daskals/A-Rectifier-Circuit-Insensitive-to-the-Angle-of-Incidence-of-Incoming-Waves-Based-on-a-Wilkinson/Publication_files/Figures/Fig3-eps-converted-to.pdf

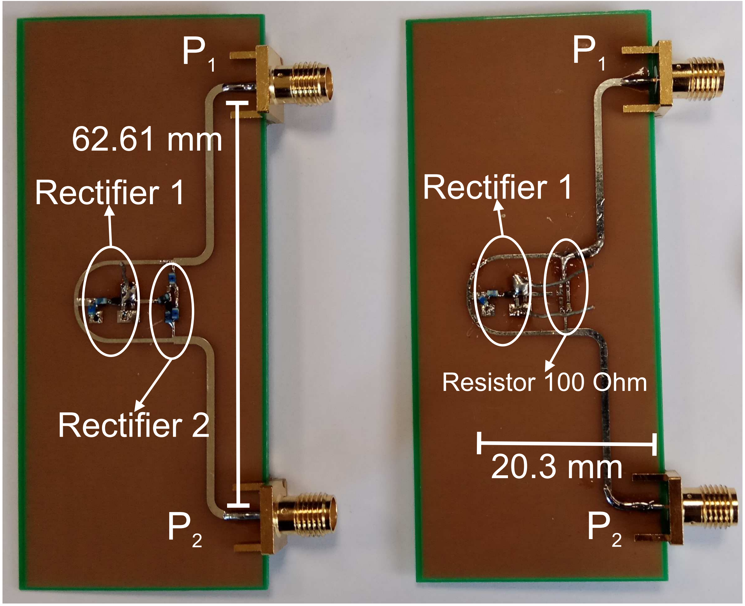
[picture p15: page 1]

Rectifier 1

Rectifier 2

Rectifier 1

Resistor 100 Ohm

62.61 mm

20 3. mm

P1

P2

P1

P2
