daskals/A-Rectifier-Circuit-Insensitive-to-the-Angle-of-Incidence-of-Incoming-Waves-Based-on-a-Wilkinson/Publication_files/Figures/Fig6-eps-converted-to.pdf

-40 | -30 | -20 | -10 | 0 | 10
Power Input (dBm)

0

10

20

30

40

Efficiency (%)
