daskals/A-Rectifier-Circuit-Insensitive-to-the-Angle-of-Incidence-of-Incoming-Waves-Based-on-a-Wilkinson/Publication_files/Figures/Fig16-eps-converted-to.pdf

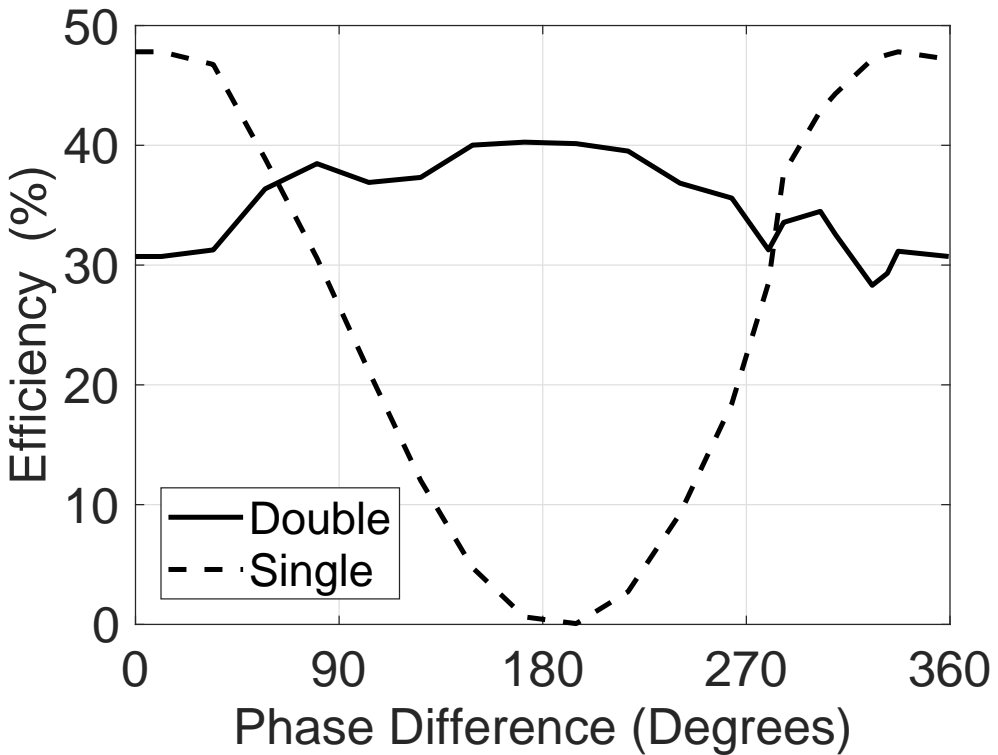
[picture p21: figure]
Phase Difference (Degrees); Efficiency (%); Double Single
