daskals/A-Rectifier-Circuit-Insensitive-to-the-Angle-of-Incidence-of-Incoming-Waves-Based-on-a-Wilkinson/Publication_files/Figures/Fig2-eps-converted-to.pdf

V

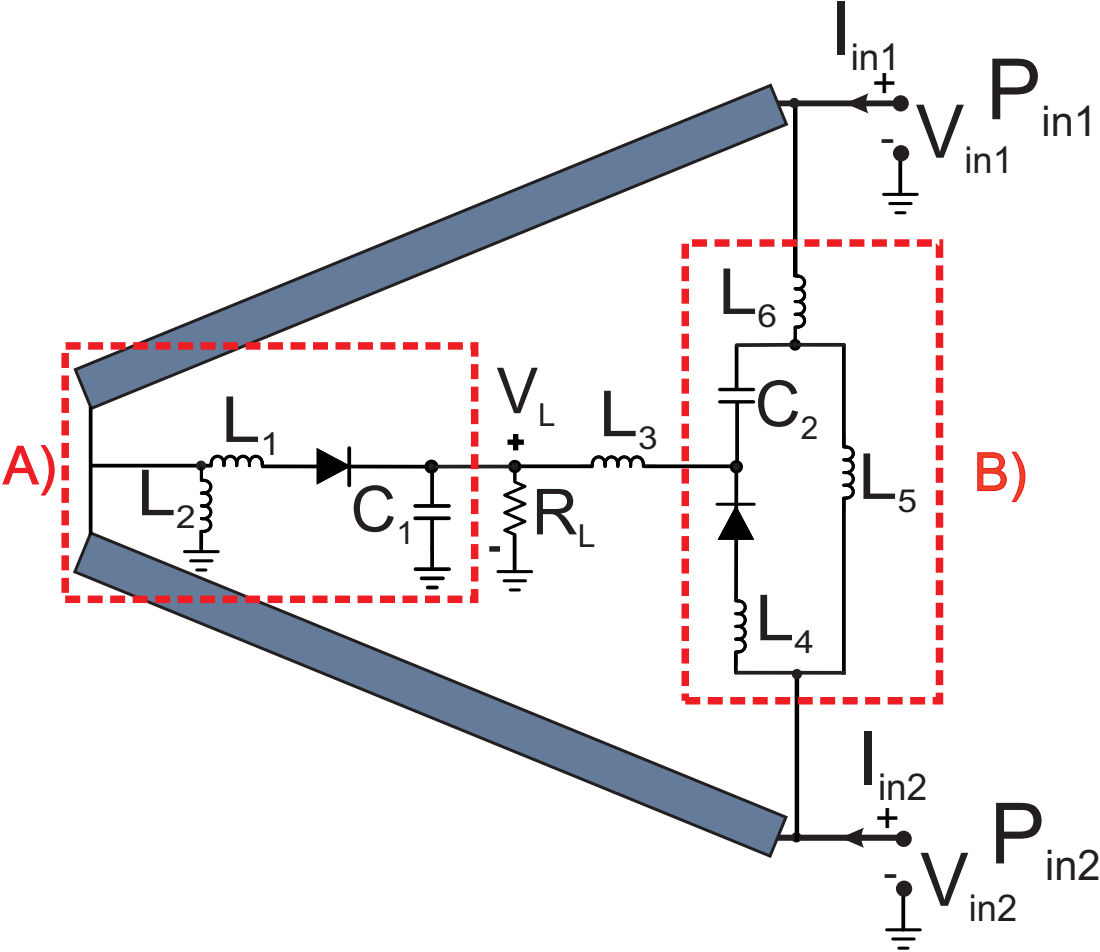
[picture p22: page 1]
Pin1; in1 Iin1; Pin2; Vin2 Iin2-
