daskals/A-Rectifier-Circuit-Insensitive-to-the-Angle-of-Incidence-of-Incoming-Waves-Based-on-a-Wilkinson/Publication_files/Figures/Fig4-eps-converted-to.pdf

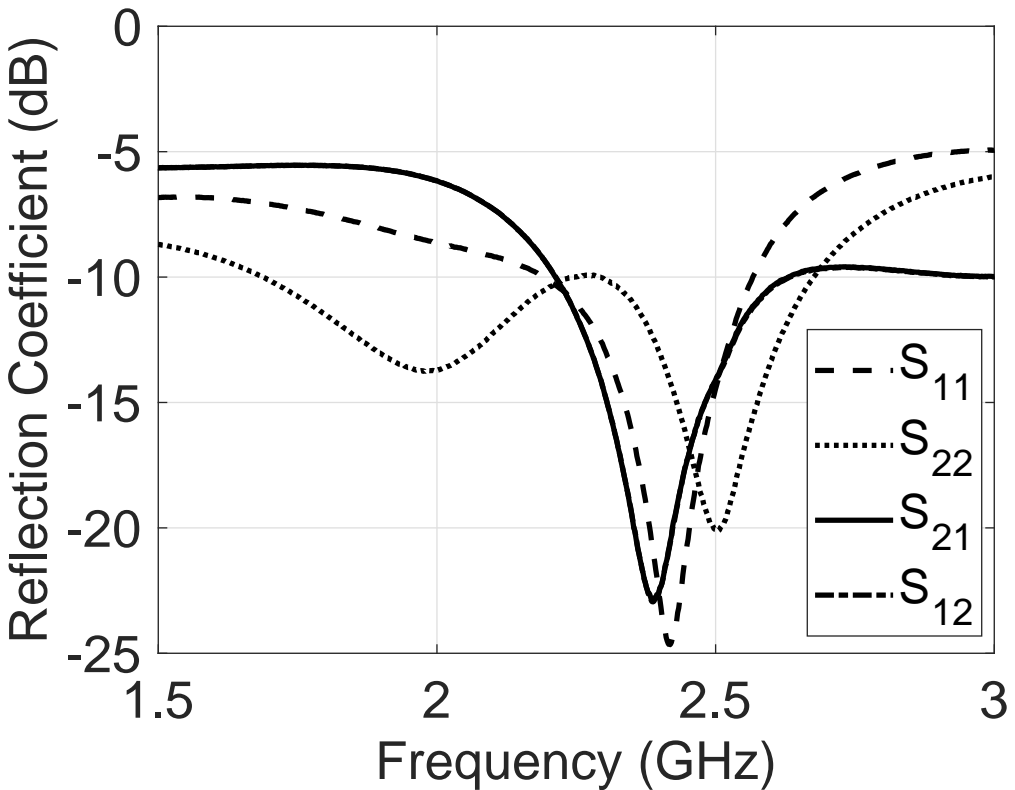
[picture p23: page 1]
Frequency (GHz)

Reflection Coefficient (dB)

S11
S22
