daskals/A-Rectifier-Circuit-Insensitive-to-the-Angle-of-Incidence-of-Incoming-Waves-Based-on-a-Wilkinson/Publication_files/Figures/Fig5-eps-converted-to.pdf

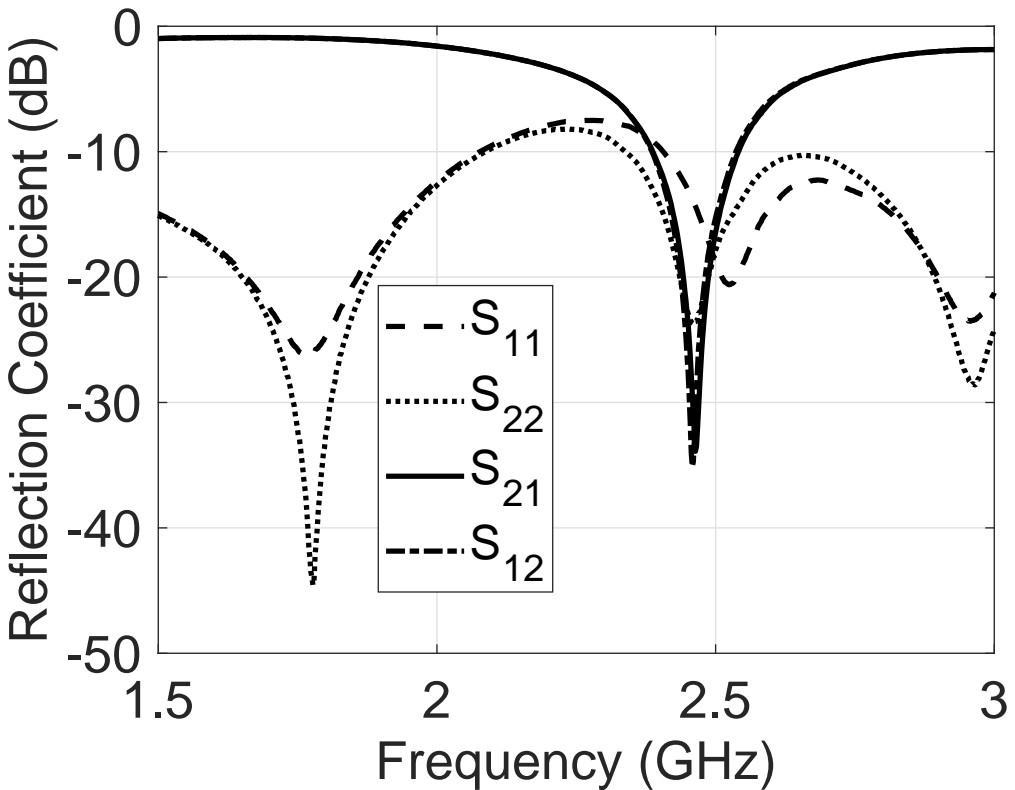
[picture p24: page 1]
Frequency (GHz)

Reflection Coefficient (dB)

S21
S12
